runningdeveloper/running-display/esp/src/config_sample.h

// Physical device information
#define DEVICE_ID "YOUR DEVICE ID"

// Interval time(ms) for sending message to IoT Hub, use this later for heath check
#define INTERVAL 2000

#define MESSAGE_MAX_LEN 256

#define SSID "YOUR SSID"
#define SSID_PASS "YOUR PASSWORD"

// pin for neopixels
#define PIN 4
#define NUMPIXELS 18

// connection string iot hub
#define CONNECTION_STRING "HostName=..."
